Eisbaeeer/Arduino.Ethernet.Zisterne/src/progress.h

/* Caractères personnalisés */
byte START_DIV_0_OF_1[8] = {
  B01111, 
  B11000,
  B10000,
  B10000,
  B10000,
  B10000,
  B11000,
  B01111
}; // Char début 0 / 1

byte START_DIV_1_OF_1[8] = {
  B01111, 
  B11000,
  B10011,
  B10111,
  B10111,
  B10011,
  B11000,
  B01111
}; // Char début 1 / 1

byte DIV_0_OF_2[8] = {
  B11111, 
  B00000,
  B00000,
  B00000,
  B00000,
  B00000,
  B00000,
  B11111
}; // Char milieu 0 / 2

byte DIV_1_OF_2[8] = {
  B11111, 
  B00000,
  B11000,
  B11000,
  B11000,
  B11000,
  B00000,
  B11111
}; // Char milieu 1 / 2

byte DIV_2_OF_2[8] = {
  B11111, 
  B00000,
  B11011,
  B11011,
  B11011,
  B11011,
  B00000,
  B11111
}; // Char milieu 2 / 2

byte END_DIV_0_OF_1[8] = {
  B11110, 
  B00011,
  B00001,
  B00001,
  B00001,
  B00001,
  B00011,
  B11110
}; // Char fin 0 / 1

byte END_DIV_1_OF_1[8] = {
  B11110, 
  B00011,
  B11001,
  B11101,
  B11101,
  B11001,
  B00011,
  B11110
}; // Char fin 1 / 1


/**
 * Fonction de configuration de l'écran LCD pour la barre de progression.
 * Utilise les caractères personnalisés de 0 à 6 (7 reste disponible).
 */
void setup_progressbar() {

  /* Enregistre les caractères personnalisés dans la mémoire de l'écran LCD */
  lcd.createChar(0, START_DIV_0_OF_1);
  lcd.createChar(1, START_DIV_1_OF_1);
  lcd.createChar(2, DIV_0_OF_2);
  lcd.createChar(3, DIV_1_OF_2);
  lcd.createChar(4, DIV_2_OF_2);
  lcd.createChar(5, END_DIV_0_OF_1);
  lcd.createChar(6, END_DIV_1_OF_1);
}
